MultipedRobotics/quadruped-AX12/docs/ax12-inside-2.jpg

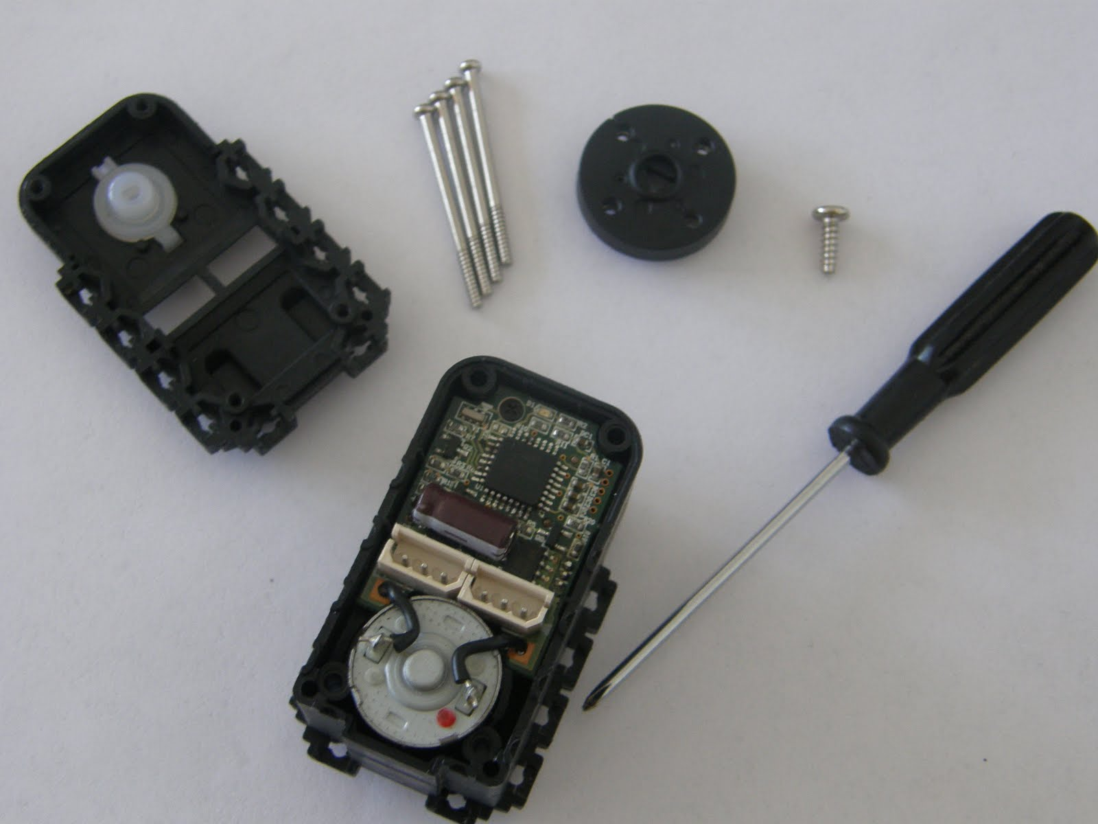
docs/ax12-inside-2.jpg
