MultipedRobotics/quadruped-AX12/docs/ax12-inside.jpg

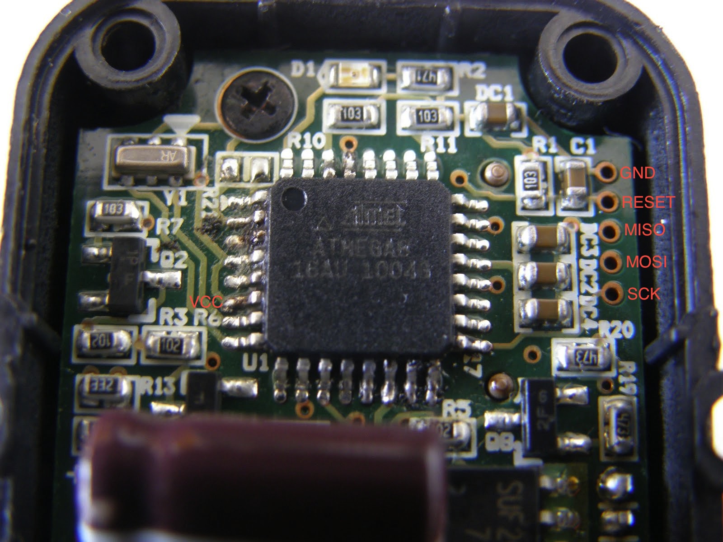
docs/ax12-inside.jpg
