MultipedRobotics/quadruped-AX12/docs/ax-12-angles.png

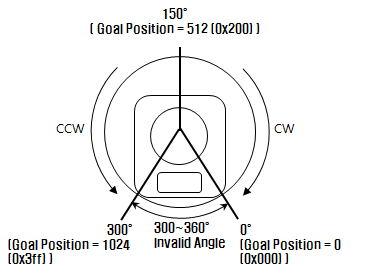
docs/ax-12-angles.png
