MultipedRobotics/quadruped-AX12/docs/ax-12-quad-servos.png

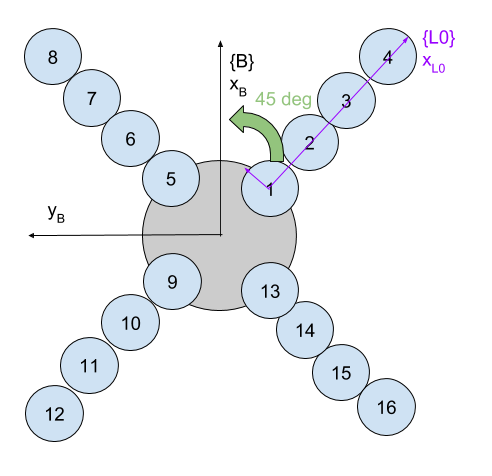
docs/ax-12-quad-servos.png
