MultipedRobotics/quadruped-AX12/docs/ax-12a.jpg

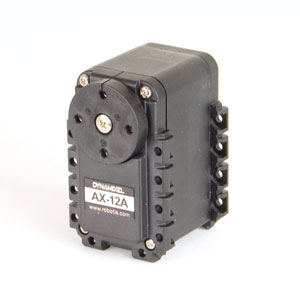
docs/ax-12a.jpg
