MultipedRobotics/quadruped-AX12/docs/cm-shift.png

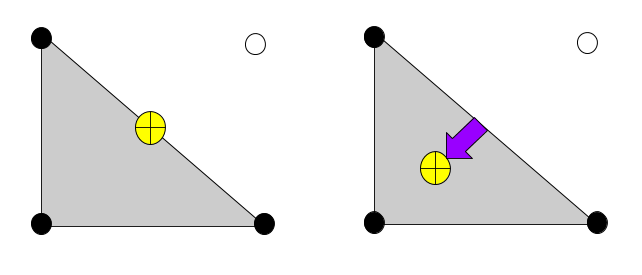
docs/cm-shift.png
