MultipedRobotics/quadruped-AX12/docs/leg-coordinate-system.png

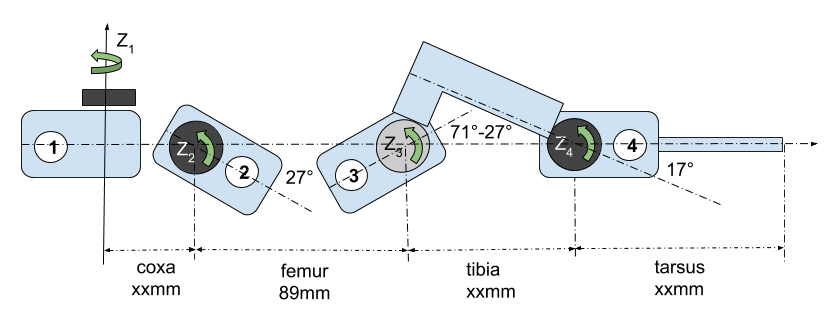
docs/leg-coordinate-system.png
