MultipedRobotics/quadruped-AX12/docs/leg-design/applsci-11-09217-g001.webp

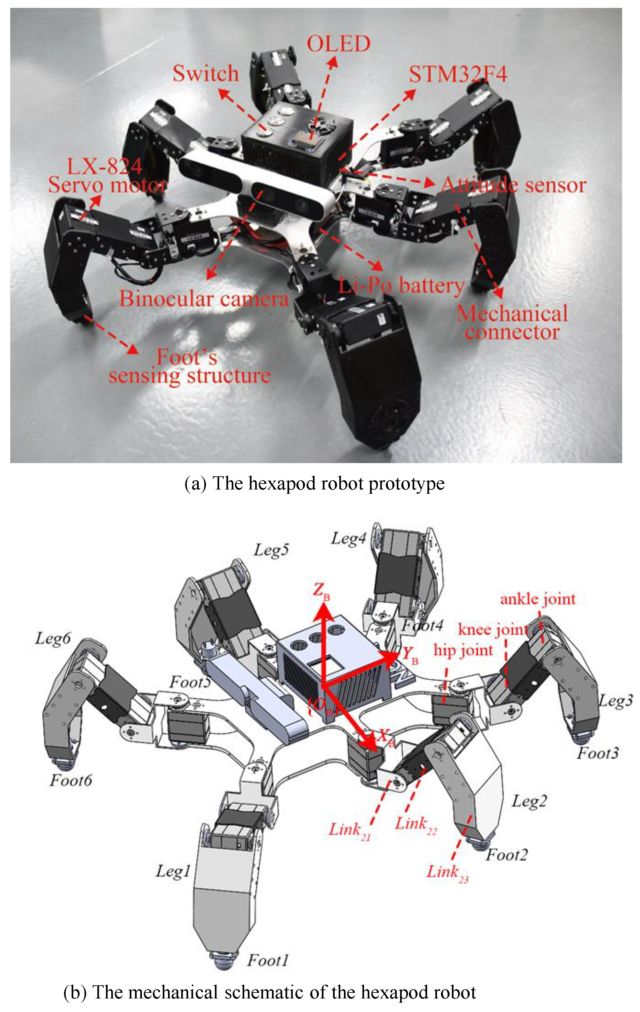
docs/leg-design/applsci-11-09217-g001.webp
