MultipedRobotics/quadruped-AX12/docs/leg.jpg

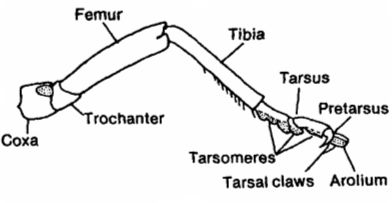
docs/leg.jpg
