MultipedRobotics/quadruped-AX12/docs/quad-sequence.png

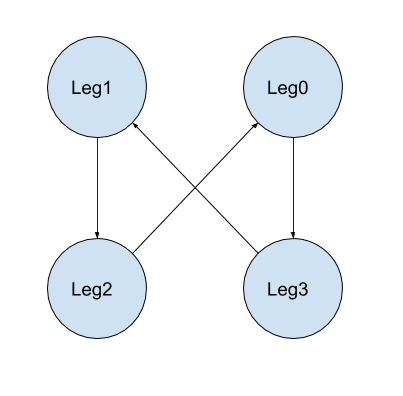
docs/quad-sequence.png
