MultipedRobotics/quadruped-AX12/docs/real-leg.jpg

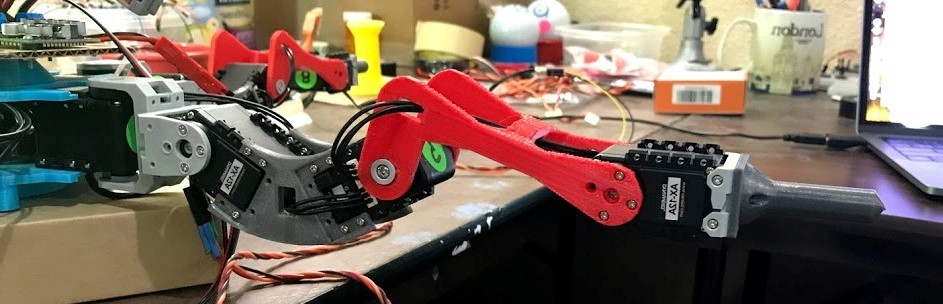
docs/real-leg.jpg
