MultipedRobotics/quadruped-AX12/docs/stand.jpg

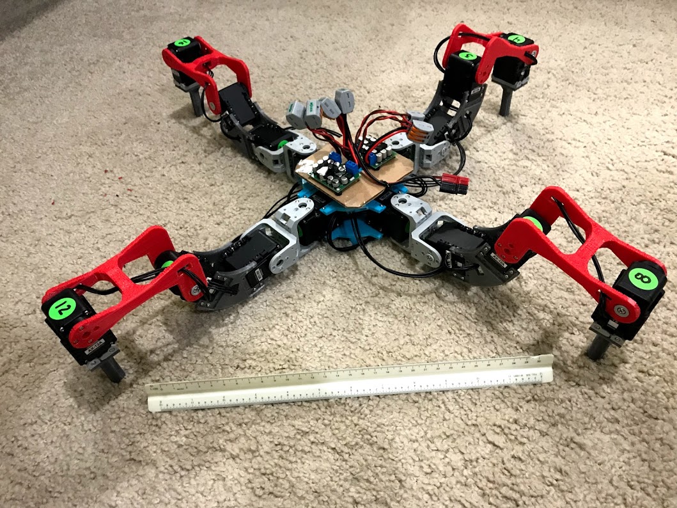
docs/stand.jpg
