MultipedRobotics/quadruped-AX12/docs/stow.jpg

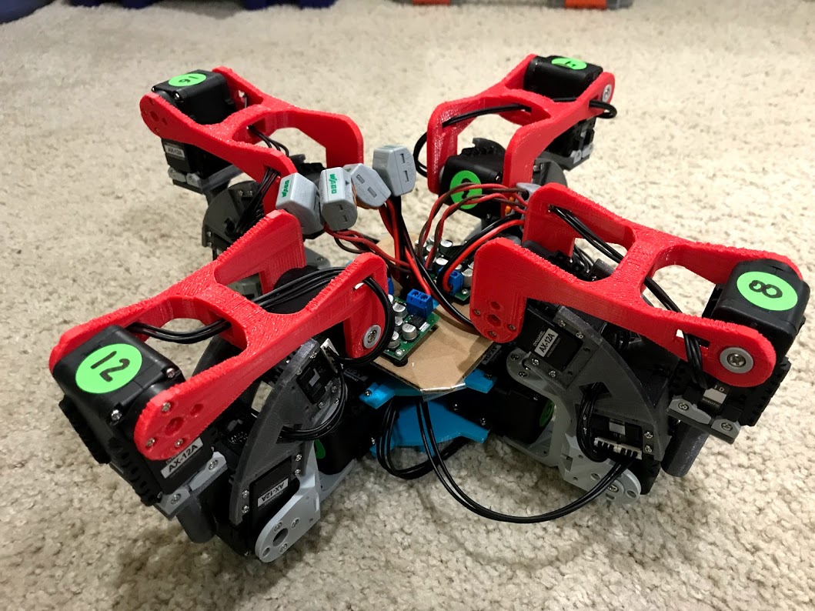
docs/stow.jpg
