MultipedRobotics/quadruped-AX12/docs/walking.png

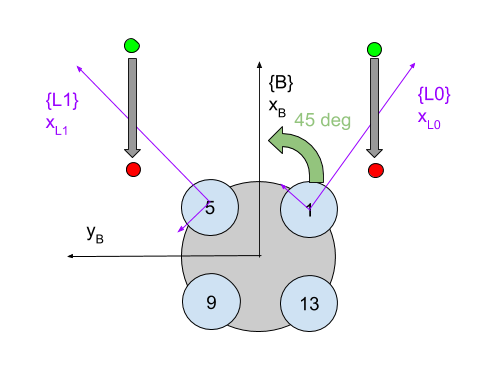
docs/walking.png
