MultipedRobotics/quadruped-AX12/electrical/power-v6/pics/bottom.png

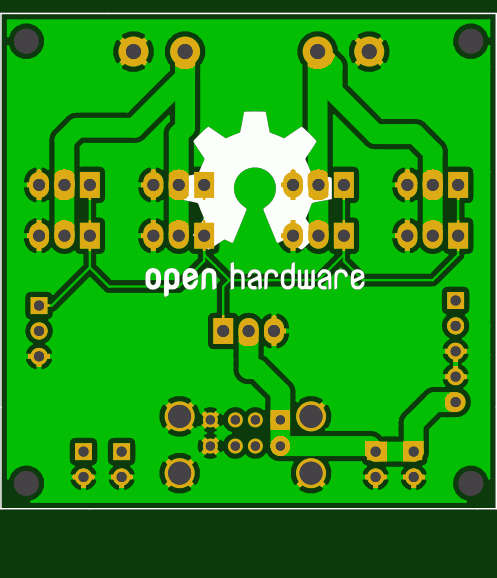
electrical/power-v6/pics/bottom.png
