MultipedRobotics/quadruped-AX12/electrical/power-v6/pics/top.png

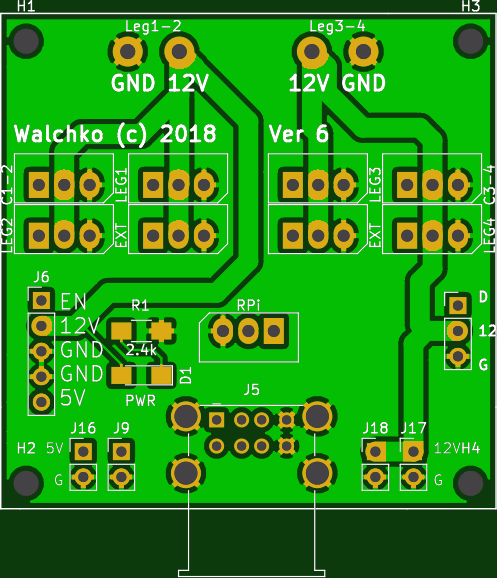
electrical/power-v6/pics/top.png
