MultipedRobotics/quadruped-AX12/electrical/rpi/pics/bottom.png

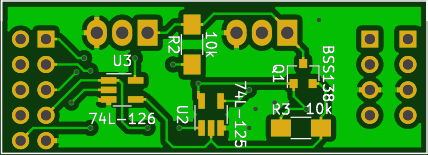
electrical/rpi/pics/bottom.png
