MultipedRobotics/quadruped-AX12/electrical/rpi/pics/top.png

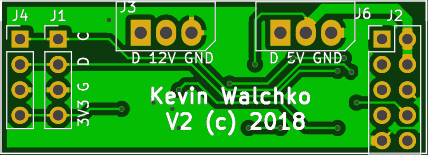
electrical/rpi/pics/top.png
