MultipedRobotics/quadruped-AX12/misc/color-tracking/ball.jpg

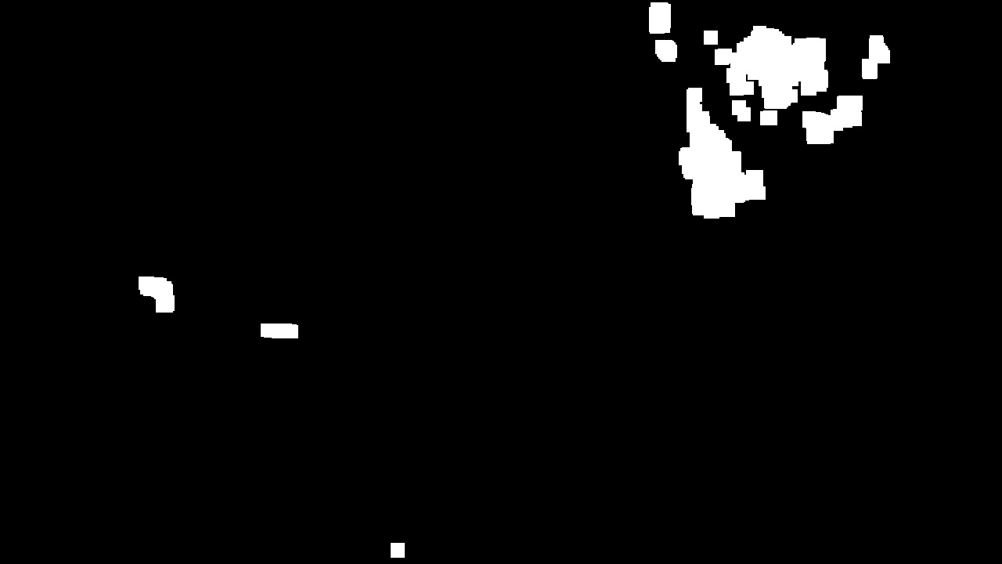
misc/color-tracking/ball.jpg
