MultipedRobotics/quadruped-AX12/misc/color-tracking/save/ball-1.png

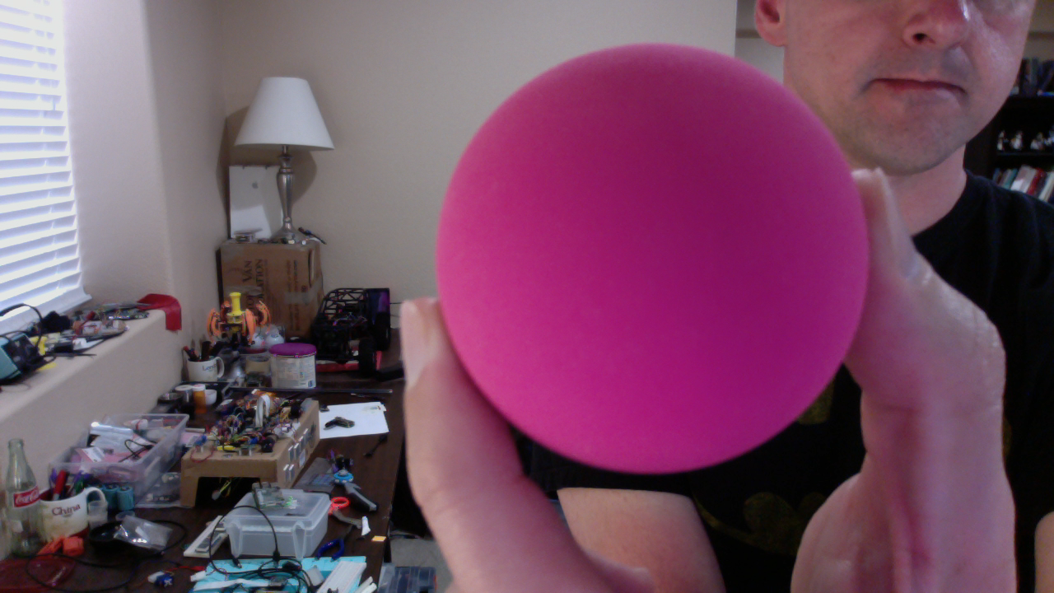
misc/color-tracking/save/ball-1.png
