MultipedRobotics/quadruped-AX12/misc/color-tracking/save/ball-2.png

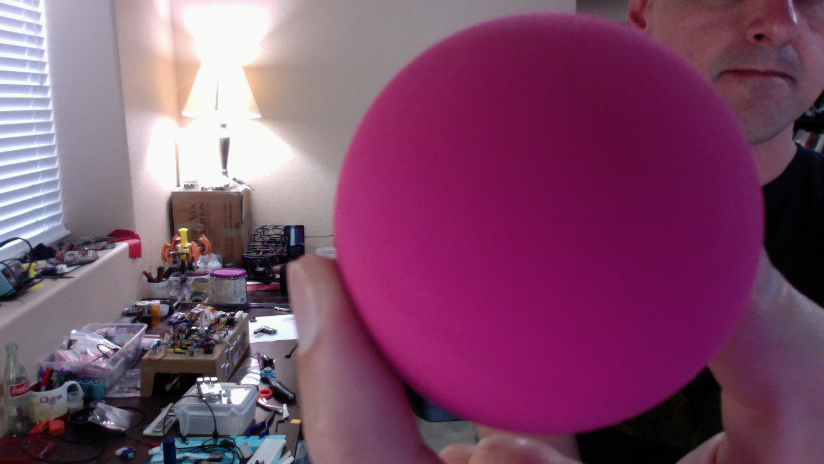
misc/color-tracking/save/ball-2.png
